MengqiS21/TECHIN515_final_project_smart_litter_box/ML screenshot/2- float32.png

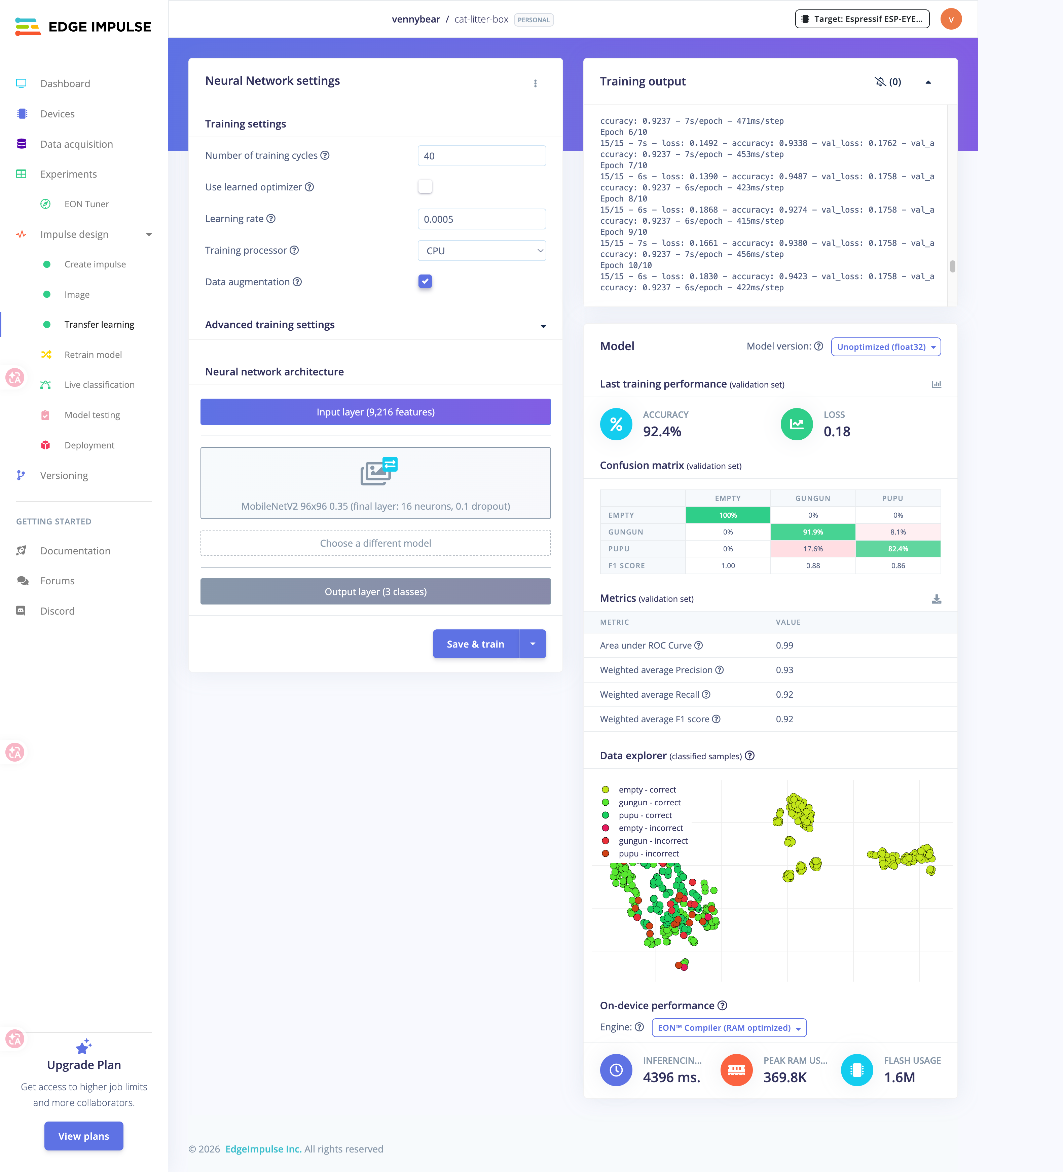
ML screenshot/2- float32.png
