MengqiS21/TECHIN515_final_project_smart_litter_box/ML screenshot/4-accuracy float32.png

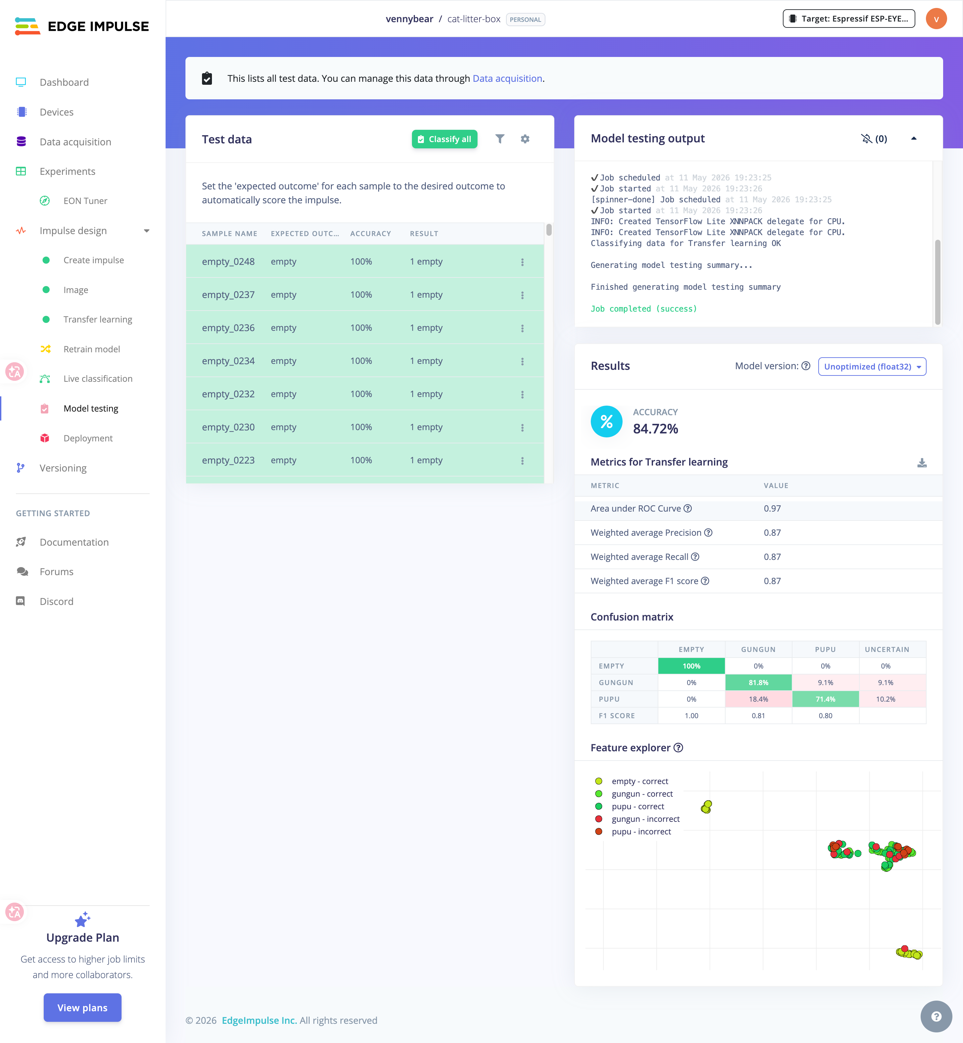
ML screenshot/4-accuracy float32.png
