MengqiS21/TECHIN515_final_project_smart_litter_box/test_report_and_photo/test3.jpg

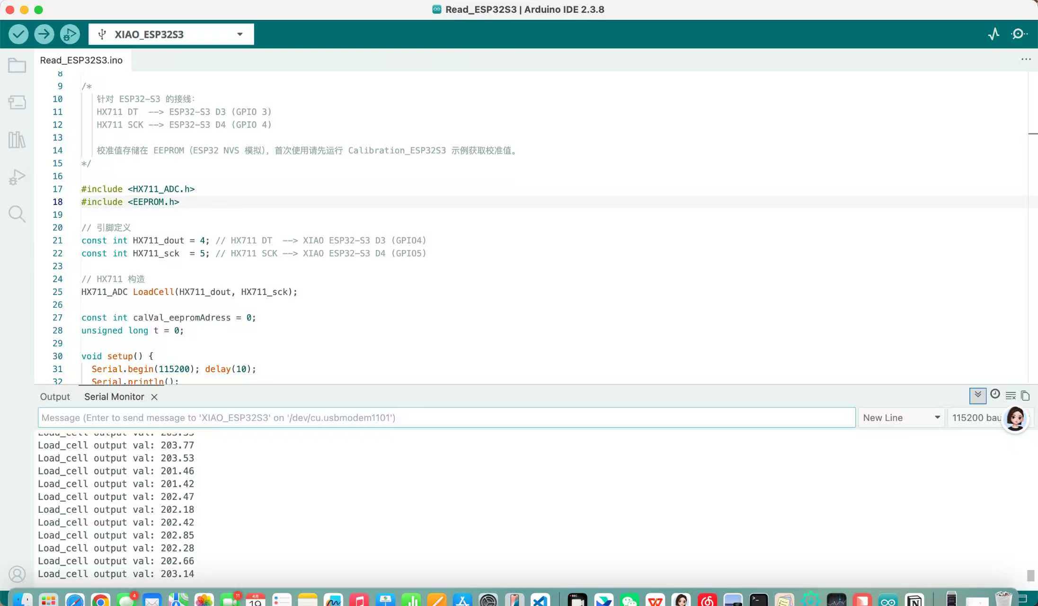
test_report_and_photo/test3.jpg
